VeiLiang/BoloPi_PCB/bolopi_F1_0.png

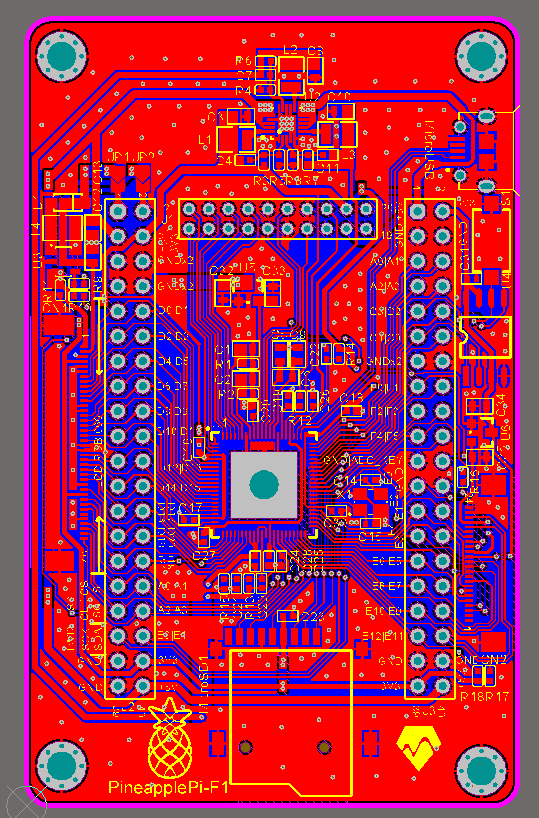
bolopi_F1_0.png
