VeiLiang/BoloPi_PCB/bolopi_F1_V2_3.png

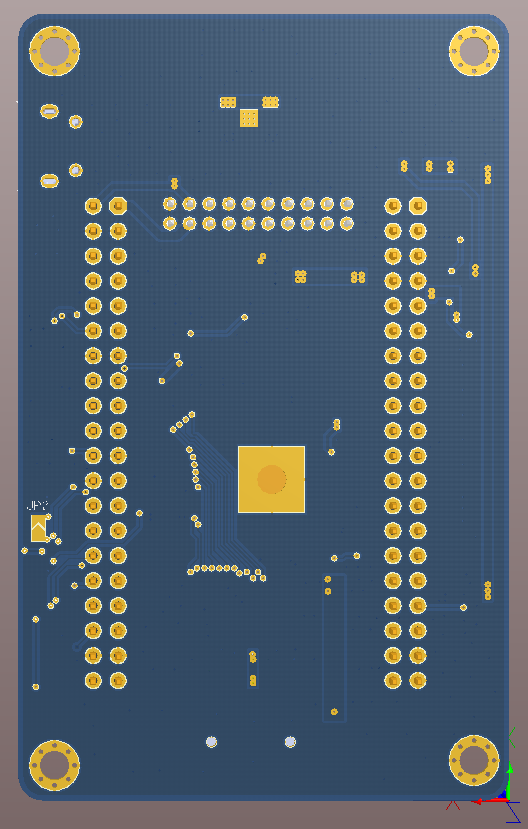
bolopi_F1_V2_3.png
